Kneckter/ATVRackEnclosure/AuxNamePlate.FCStd

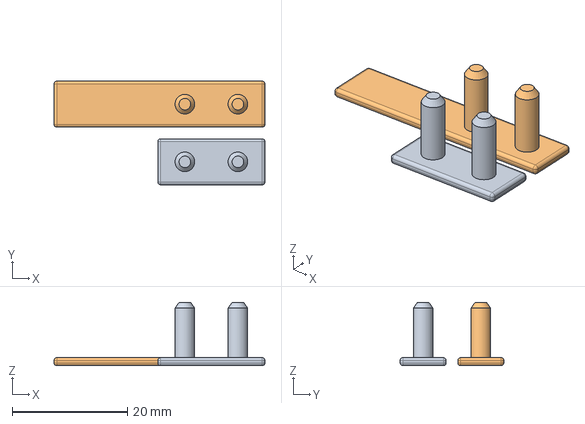
[picture p30: CAD file, 2022-09-24]
AuxNamePlate.FCStd
36.6 x 18.0 x 11.0 mm
x96_NamePlate_Short
x96_NamePlate_Long
