Kneckter/ATVRackEnclosure/x96_AuxNamePlate_Short.stl

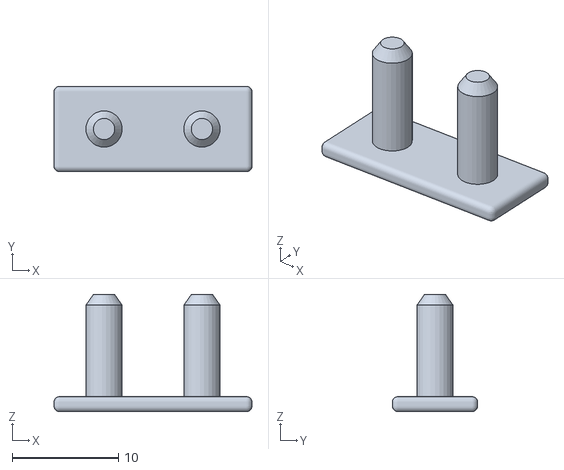
[picture p31: CAD file, 2022-09-24]
x96_AuxNamePlate_Short.stl
18.6 x 8.00 x 11.0
