Kneckter/ATVRackEnclosure/x96_AuxNamePlate_Long.stl

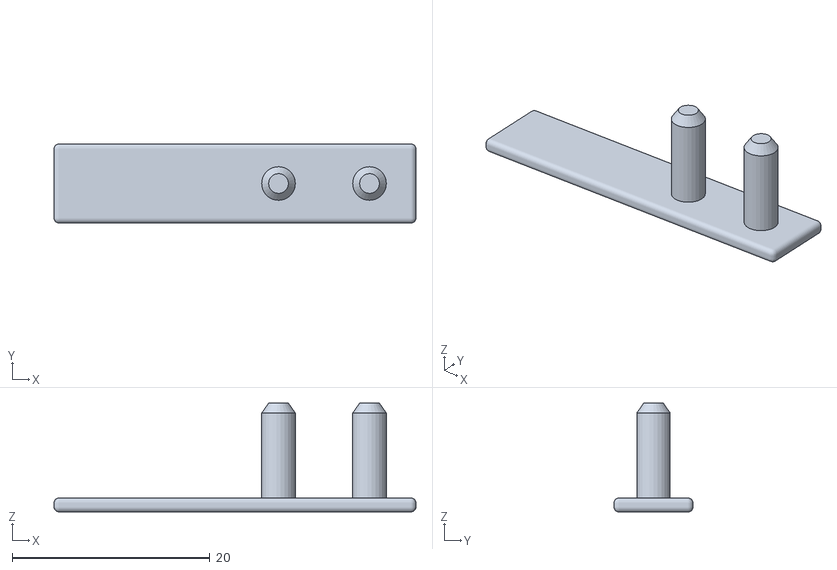
[picture p32: CAD file, 2022-09-24]
x96_AuxNamePlate_Long.stl
36.6 x 8.00 x 11.0
