Kneckter/ATVRackEnclosure/x96_Cage_Right.stl

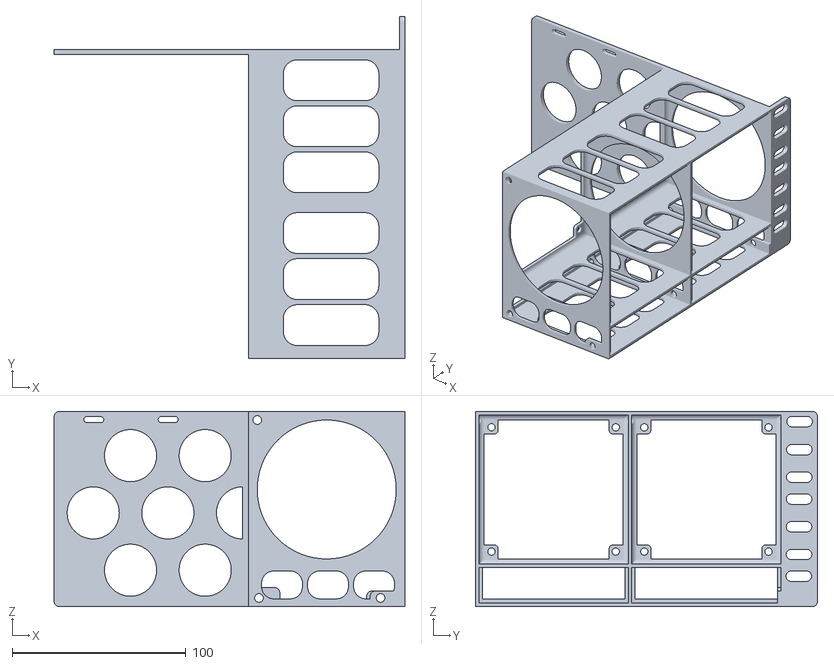
[picture p33: CAD file, 2022-09-12]
x96_Cage_Right.stl
202.0 x 197.0 x 112.5
